CalgaryToSpace/CTS-Solar-Panel-Load-Tester/Solar Panel LT Spice Simulation.asc

B1: bi; I=V(illu)/1000*Iph
D1: diode; SolarDiode
I1: current; PULSE(0 1 0 1 1); load
R1: res; {Rsh}
R2: res; {Rs}
R3: res; 100Meg
V1: voltage; 1000
Named nets: 0, v+, v-, illu
.model solardiode d(is=io n=a_n tref=temp)
.param rs=1
.param rsh=10k
.param iph=1
.param io=1e-6
.param a_n=10
.tran 1
